beauahill/AlgaeReactor/openscad/lid_threaded.scad

// Lid for the threaded printed body: flange is narrow enough to sit inside the ring, no rod holes.
use <lid.scad>
lid(threaded = true);
