beauahill/AlgaeReactor/openscad/printed_body_threaded.scad

// Option B2: printed body with an external thread at the top for the retaining ring.
use <printed_body.scad>
printed_body(threaded = true);
